erlerobot/smart_motor/AVR_OpenServo_V3-dev/adc.c

/*
    Copyright (c) 2006 Michael P. Thompson <mpthompson@gmail.com>

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
    $Id$
*/

#include <inttypes.h>
#include <avr/io.h>
#include <avr/interrupt.h>

#include "openservo.h"
#include "config.h"
#include "adc.h"
#include "timer.h"

//
// ATmega168
// =========
//
// The 10-bit Analog to Digital Converter (ADC) on the ATmega MCU is used
// to provide power and position feedback from the servo circuitry.  The
// analog inputs are assigned as follows:
//
//  ADC0 (PC0) - Motor Current
//  ADC1 (PC1) - Battery Voltage
//  ADC2 (PC2) - Position
//  ADC3 (PC3) - Temperature
//  ADC7 (PC7) - Back EMF


// Globals used to maintain ADC state and values.
volatile uint8_t adc_power_ready;
volatile uint16_t adc_power_value;
volatile uint8_t adc_position_ready;
volatile uint16_t adc_position_value;
#if BACKEMF_ENABLED
volatile uint8_t adc_backemf_ready;
volatile uint16_t adc_backemf_value;
#endif
#if TEMPERATURE_ENABLED
volatile uint8_t adc_temperature_ready;
volatile uint16_t adc_temperature_value;
#endif

void adc_init(void)
// Initialize ADC conversion for reading current monitoring and position.
{
    // Initialize flags and values.
    adc_power_ready = 0;
    adc_power_value = 0;
    adc_position_ready = 0;
    adc_position_value = 0; 
#if BACKEMF_ENABLED
    adc_backemf_ready = 0;
    adc_backemf_value = 0;
#endif
#if TEMPERATURE_ENABLED
    adc_temperature_ready = 0;
    adc_temperature_value = 0;
#endif

    // Make sure ports PC0 (ADC0), PC1 (ADC1) and PC2 (ADC2) are set low.
    PORTC &= ~((1<<PC0) | (1<<PC1) | (1<<PC2));

    // Disable digital input for ADC0, ADC1 and ADC2.
    DIDR0 |= (1<<ADC0D) | (1<<ADC1D) |(1<<ADC2D);

    // Set the ADC multiplexer selection register.
    ADMUX = (0<<REFS1) | (1<<REFS0) |                       // Select AVCC as voltage reference.
            (0<<ADLAR) |                                    // Keep high bits right adjusted.
            ADC_CHANNEL_POSITION;                           // Position as the first channel to sample.

    // Set the ADC control and status register B.
    ADCSRB = (0<<ADTS2) | (1<<ADTS1) | (1<<ADTS0);          // Timer/Counter0 Compare Match A.

    // Set the ADC control and status register A.
    ADCSRA = (1<<ADEN) |                                    // Enable ADC.
             (0<<ADSC) |                                    // Don't start yet, will be triggered manually.
             (0<<ADATE) |                                   // Don't start auto triggering.
             (1<<ADIE) |                                    // Activate ADC conversion complete interrupt.
             ADPS;											// Prescale -- see above.
}

void adc_start(uint8_t channel)
// Initialise the adc sample on the first channel
{
    // Set the ADC multiplexer selection register.
    ADMUX = (0<<REFS1) | (1<<REFS0) |                       // Select AVCC as voltage reference.
            (0<<ADLAR) |                                    // Keep high bits right adjusted.
            channel;                           // Position as the first channel to sample.

    // Start the ADC reading of the position channel.
    ADCSRA |= (1<<ADSC);
}

SIGNAL(ADC_vect)
// Handles ADC interrupt. This runs as an interrupting self triggering mechanism sampling selected channels
// When interrupted with position, it moved initiates the power sampling, which when interrupted initiates
// the other channels in a chain. The Back EMF is not sampled as part of the
// cascade, as this is handled by the backemf module.
{
    // Read the 10-bit ADC value.
    uint16_t new_value = ADCW;

    // Which channel is being read?
    switch (ADMUX & 0x0f)
    {

        case ADC_CHANNEL_POSITION:

            // Save the new position value.
            adc_position_value = new_value;

            // Flag the position value as ready.
            adc_position_ready = 1;

            // Set the ADC multiplexer selection register.
            ADMUX = (0<<REFS1) | (1<<REFS0) |                       // Select AVCC as voltage reference.
                    (0<<ADLAR) |                                    // Keep high bits right adjusted.
                    ADC_CHANNEL_CURRENT;                            // Power as the next channel to sample.

            // Start the ADC of the power channel now
            ADCSRA |= (1<<ADSC);

            break;


        case ADC_CHANNEL_CURRENT:

            // Save the new power value.
            adc_power_value = new_value;

            // Flag the power value as ready.
            adc_power_ready = 1;

            // Set the ADC multiplexer selection register.
            int channel;

#if TEMPERATURE_ENABLED
            channel = ADC_CHANNEL_TEMPERATURE;                        // Temperature as the next channel to sample.
#elif BATTERY_ENABLED
            channel = ADC_CHANNEL_BATTERY;                            // Sample the battery channel next
#else
            break;
#endif
            ADMUX = (0<<REFS1) | (1<<REFS0) |                       // Select AVCC as voltage reference.
                    (0<<ADLAR) | channel;                           // Keep high bits right adjusted.

            // Start the ADC of the temperature channel now
            ADCSRA |= (1<<ADSC);


            break;

#if TEMPERATURE_ENABLED
        case ADC_CHANNEL_TEMPERATURE:

            // Save the temperature value
            adc_temperature_value = new_value;

            // Fag the temperature value as ready
            adc_temperature_ready = 1;
#if BATTERY_ENABLED
            // Now sample the battery voltage
            // Set the ADC multiplexer selection register.
            ADMUX = (0<<REFS1) | (1<<REFS0) |                       // Select AVCC as voltage reference.
                    (0<<ADLAR) |                                    // Keep high bits right adjusted.
                    ADC_CHANNEL_BATTERY;                            // Battery voltage as the next channel to sample.

            // Start the ADC of the voltage channel now
            ADCSRA |= (1<<ADSC);
#endif
            break;
#endif
#if BATTERY_ENABLED
        case ADC_CHANNEL_BATTERY:

            // Save voltage value to registers
            registers_write_word(REG_VOLTAGE_HI, REG_VOLTAGE_LO, new_value);

            break;
#endif
#if BACKEMF_ENABLED
        case ADC_CHANNEL_BACKEMF:

            adc_backemf_ready = 1;

            adc_backemf_value = new_value;

            break;
#endif
    }
}
