erlerobot/smart_motor/AVR_OpenServo_V3-dev/twi.c

/*
    Copyright (c) 2006 Michael P. Thompson <mpthompson@gmail.com>
        Portions of this code 
    Copyright (c) 2007 Barry Carter <barry.carter@gmail.com>


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
    $Id$
*/

#include <inttypes.h>
#include <avr/io.h>
#include <avr/interrupt.h>

#include "openservo.h"
#include "config.h"
#include "registers.h"
#include "twi.h"
#include "banks.h"

//////////////////////////////////////////////////////////////////
///////////////// Driver Buffer Definitions //////////////////////
//////////////////////////////////////////////////////////////////
// 1,2,4,8,16,32,64,128 or 256 bytes are allowed buffer sizes

#define TWI_RX_BUFFER_SIZE (4)
#define TWI_RX_BUFFER_MASK (TWI_RX_BUFFER_SIZE - 1)

#if (TWI_RX_BUFFER_SIZE & TWI_RX_BUFFER_MASK)
        #error TWI RX buffer size is not a power of 2
#endif

#define TWI_CHK_WRITE_BUFFER_SIZE (16)
#define TWI_CHK_WRITE_BUFFER_MASK (TWI_CHK_WRITE_BUFFER_SIZE - 1)

#if (TWI_CHK_WRITE_BUFFER_SIZE & TWI_CHK_WRITE_BUFFER_MASK)
        #error TWI CHK WRITE buffer size is not a power of 2
#endif

//////////////////////////////////////////////////////////////////

// TWI acknowledgment values.
#define TWI_ACK                             (0x00)
#define TWI_NAK                             (0x01)

// Data state values.
#define TWI_DATA_STATE_COMMAND              (0x00)
#define TWI_DATA_STATE_DATA                 (0x01)
#if TWI_CHECKED_ENABLED
#define TWI_DATA_STATE_CHECKED_COUNTING     (0x02)
#define TWI_DATA_STATE_CHECKED_ADDRESS      (0x03)
#define TWI_DATA_STATE_CHECKED_DATA         (0x04)
#endif

static volatile uint8_t twi_address;
static volatile uint8_t twi_data_state;
static volatile uint8_t twi_overflow_state;

static volatile uint8_t twi_rxhead;
static volatile uint8_t twi_rxtail;
static uint8_t twi_rxbuf[TWI_RX_BUFFER_SIZE];

#if TWI_CHECKED_ENABLED
// For checked writing send in the format of  [i2c addr][0x81][data length][data address][data]...[data] [checksum value] [checksum value]
// For a checked read use  [i2c_addr][0x81][data length][data address] SLA+R [data][data]...[checksum value]
// Checksum is defined as data length + data_address + data[n]
// To verify a write was successful, write the header above, and see if it nacks. nack is failure of checksum.
static uint8_t twi_chk_count;            // current byte in transaction
static uint8_t twi_chk_count_target;     // How many bytes are we reading/writing
static uint8_t twi_chk_sum;              // Accumulator for checksum
static uint8_t twi_chk_write_buffer[TWI_CHK_WRITE_BUFFER_SIZE];
#endif

static uint8_t twi_registers_read(uint8_t address)
// Read the byte from the specified register.  This function handles the
// reading of special registers such as unused registers, redirect and
// redirected registers.
{
    // Mask the most significant bit of the address.
    address &= 0x7F;

    // Are we reading a normal register?
    if (address <= MAX_WRITE_PROTECT_REGISTER)
    {
#if ROLLING_SUBTYPE
        if (address == REG_DEVICE_SUBTYPE)
        {
            return registers_subtype_cycle();
        }
#endif
        // Yes. Complete the read.
        return registers_read_byte(address);
    }

    // Are we reading an unused register.
    if (address <= MAX_UNUSED_REGISTER)
    {
        // Block the read.
        return 0;
    }

    // Are we reading a bank register? 
    if (address <= MAX_BANK_REGISTER)
    {
        // Conditional bank functions
        switch(banks_selected_bank())
        {
            case REDIRECTED_BANK:
                // Are we reading a redirect register.
                if (address <=  MIN_BANK_REGISTER + MAX_REDIRECT_REGISTER)
                {
                    // Yes. Complete the read.
                    return banks_read_byte(REDIRECTED_BANK, address -  MIN_BANK_REGISTER);
                }

                // Are we reading a redirected register?
                if (address <= MIN_BANK_REGISTER + MAX_REDIRECTED_REGISTER)
                {
                    // Adjust address to reference appropriate redirect register.
                    address = address - (MIN_BANK_REGISTER + MIN_REDIRECTED_REGISTER);
                    // Get the address from the redirect register.
                    address = banks_read_byte(REDIRECTED_BANK, address);
                    // Prevent infinite recursion.
                    if (address <= MIN_BANK_REGISTER + MAX_REDIRECT_REGISTER)
                    {
                        // Recursively read redirected address.
                        return twi_registers_read(address);
                    }
                }
                break;
            default:
                break;
        }
        // Defaults to returning the register n the bank array
        return banks_read_byte(banks_selected_bank(), address-MIN_BANK_REGISTER);
    }

    // All other reads are blocked.
    return 0;
}


static void twi_registers_write(uint8_t address, uint8_t data)
// Write non-write protected registers.  This function handles the
// writing of special registers such as unused registers, redirect and
// redirected registers.
{
    // Mask the most significant bit of the address.
    address &= 0x7F;

    // Are we writing a read only register?
    if (address <= MAX_READ_ONLY_REGISTER)
    {
        // Yes. Block the write.
        return;
    }

    // Are we writing a read/write register?
    if (address <= MAX_READ_WRITE_REGISTER)
    {
        // Check that the bank selection is in range
        if (address == REG_BANK_SELECT)
        {
            if (data >= MAX_BANKS)
            {
                // Set the bank number to the maximum
                data = MAX_BANKS-1;
            }
        }

        // Yes. Complete the write.
        registers_write_byte(address, data);

        return;
    }

    // Is writing to the upper registers disabled?
    if (registers_is_write_disabled() && (address <= MAX_WRITE_PROTECT_REGISTER))
    {
        // Yes. Block the write.
        return;
    }

    // Are we writing a write protected register?
    if (address <= MAX_WRITE_PROTECT_REGISTER)
    {
        // Yes. Complete the write if writes are enabled.
        registers_write_byte(address, data);

        return;
    }

    // Are we writing an unused register.
    if (address <= MAX_UNUSED_REGISTER)
    {
        // Yes. Block the write.
        return;
    }

    //TODO check to see if we have writes enabled/disabled
    // Are we writing a bank register? 
    if (address <= MAX_BANK_REGISTER)
    {
        switch(banks_selected_bank())
        {
            case BANK_0:
                break;
            case BANK_1:
                // Are we writing to the configuration bank while writes are disabled?
                if (registers_is_write_disabled())
                    return;
                break;
            case REDIRECTED_BANK:

                // Are we writing a redirect register.
                if (address <= MIN_BANK_REGISTER + MAX_REDIRECT_REGISTER)
                {
                    // Yes. Complete the write.
                    banks_write_byte(REDIRECTED_BANK, address - MIN_BANK_REGISTER, data);

                    return;
                }

                // Are we writing a redirected register?
                if (address <= MIN_BANK_REGISTER + MAX_REDIRECTED_REGISTER)
                {
                    // Adjust address to reference appropriate redirect register.
                    address = address - (MIN_BANK_REGISTER + MIN_REDIRECTED_REGISTER);

                    // Get the address from the redirect register.
                    address = banks_read_byte(REDIRECTED_BANK, address);

                    // Prevent infinite recursion.
                    if (address <= MIN_BANK_REGISTER + MAX_REDIRECT_REGISTER)
                    {
                        // Recursively write redirected address.
                        twi_registers_write(address, data);

                        return;
                    }
                }
                break;
            default:
                break;
        }
        return banks_write_byte(banks_selected_bank(), address-MIN_BANK_REGISTER, data);
    }

    // All other writes are blocked.
    return;
}


#if TWI_CHECKED_ENABLED
static void twi_write_buffer(void)
// Write the recieve buffer to memory.
{
    // Loop over the data within the write buffer.
    for (twi_chk_count = 0; twi_chk_count < twi_chk_count_target; twi_chk_count++)
    {
        // Write the data to the addressed register.
        twi_registers_write(twi_address, twi_chk_write_buffer[twi_chk_count & TWI_CHK_WRITE_BUFFER_MASK]);

        // Increment to the next address.
        ++twi_address;
    }
}
#endif


static uint8_t twi_read_data()
// Handle checked/non-checked read of data.
{
    // By default read the data to be returned.
    uint8_t data = twi_registers_read(twi_address);

#if TWI_CHECKED_ENABLED
    // Are we handling checked data?
    if (twi_data_state == TWI_DATA_STATE_CHECKED_DATA)
    {
        // Have we reached the end of the read?
        if (twi_chk_count < twi_chk_count_target)
        {
            // Add the data to the check sum.
            twi_chk_sum += data;

            // Increment the check sum data count.
            ++twi_chk_count;

            // Increment the address.
            ++twi_address;
        }
        else
        {
            // Replace the data with the checksum.
            data = twi_chk_sum;
        }
    }
    else
    {
        // Increment the address.
        ++twi_address;
    }
#else
    // Increment the address.
    ++twi_address;
#endif

    return data;
}


static uint8_t twi_write_data(uint8_t data)
// Handle checked/non-checked write of data or command.
{
    // By default, return ACK from write.
    uint8_t ack = TWI_ACK;

    // Handle the write depending on the write state.
    switch (twi_data_state)
    {
        case TWI_DATA_STATE_COMMAND:

            // This is a byte.
            if (data < TWI_CMD_RESET)
            {
                // Capture the address.
                twi_address = data;

                // Update the write state.
                twi_data_state = TWI_DATA_STATE_DATA;
            }
#if TWI_CHECKED_ENABLED
            else if (data == TWI_CMD_CHECKED_TXN)
            {
                // Update the write state.
                twi_data_state = TWI_DATA_STATE_CHECKED_COUNTING;
            }
#endif
            else
            {
                // Handle the command asynchronously.
                twi_rxhead = (twi_rxhead + 1) & TWI_RX_BUFFER_MASK;
                twi_rxbuf[twi_rxhead] = data;
            }

            break;

        case TWI_DATA_STATE_DATA:

            // Write the data to the addressed register.
            twi_registers_write(twi_address, data);

            // Increment to the next address.
            ++twi_address;

            break;

#if TWI_CHECKED_ENABLED
        case TWI_DATA_STATE_CHECKED_COUNTING:

            // Read in the count (Make sure it's less than the max count)
            // and start the checksum
            twi_chk_sum = twi_chk_count_target = data & TWI_CHK_WRITE_BUFFER_MASK;

            // Clear the checksum and count.
            twi_chk_count = 0;

            // Update the write state.
            twi_data_state = TWI_DATA_STATE_CHECKED_ADDRESS;

            break;

        case TWI_DATA_STATE_CHECKED_ADDRESS:

            // Capture the address and include it in the checksum
            twi_chk_sum += twi_address = data;

            // Update the write state.
            twi_data_state = TWI_DATA_STATE_CHECKED_DATA;

            break;

        case TWI_DATA_STATE_CHECKED_DATA:

            // Have we reached the end of the write?
            if (twi_chk_count < twi_chk_count_target)
            {
                // No. Write the data to the checksum buffer
                twi_chk_write_buffer[twi_chk_count & TWI_CHK_WRITE_BUFFER_MASK] = data;

                // Add the data to the checksum.
                twi_chk_sum += data;

                // Increment the check sum data count.
                ++twi_chk_count;
            }
            else
            {
                // Verify the checksum
                if (data == twi_chk_sum)
                {
                    // Write the checksum buffer to addressed registers.
                    twi_write_buffer();
                }
                else
                {
                    // Checksum failed so return NACK.
                    ack = TWI_NAK;
                }
            }

            break;
#endif
    }

    return ack;
}

// General call functions. General call allows you to send a data packet to all 
// servos at the same time. In order to use the general call support of the AVR you 
// address the OpenServos at address 0x00. Every servo will respond to the general
// call request and act appropriately. 
// You can specify groups to use with the broadcast request to allow for the servo
// to respond to different requests, or you can allow all to respond to a single
// request.

void general_call_enable(void)
// Enable general call broadcast support at address 0x00
{
    TWAR |=  (1<<TWGCE);       // Enable general call at address 0x00

    uint8_t flags_lo = registers_read_byte(REG_FLAGS_LO);

    // Enable PWM to the servo motor.
    registers_write_byte(REG_FLAGS_LO, flags_lo | (1<<FLAGS_LO_GENERALCALL_ENABLED));
}

void general_call_disable(void)
// Disable general call support.
{
    TWAR &= ~(1<<TWGCE);                      // disable general call

    uint8_t flags_lo = registers_read_byte(REG_FLAGS_LO);

    registers_write_byte(REG_FLAGS_LO, flags_lo  & ~(1<<FLAGS_LO_GENERALCALL_ENABLED));
}

void general_call_start_reset(void)
// Remove the flag that waits for the broadcast request
{
    uint8_t flags_lo = registers_read_byte(REG_FLAGS_LO);

    // Disable the general call wait flag
    registers_write_byte(REG_FLAGS_LO, flags_lo  & ~(1<<FLAGS_LO_GENERALCALL_START));

    // reset the group call register
    registers_write_byte(REG_GENERAL_CALL_GROUP_START, 0);
}

void general_call_start_move(void)
// Start the move by broadcasting at address 0x00
{
    uint8_t flags_lo = registers_read_byte(REG_FLAGS_LO);

    registers_write_byte(REG_FLAGS_LO, flags_lo | (1<<FLAGS_LO_GENERALCALL_START));
}

void general_call_start_wait(void)
// Set the servo into wait mode. We will wait for the broadcast before move
{
    uint8_t flags_lo = registers_read_byte(REG_FLAGS_LO);

    registers_write_byte(REG_FLAGS_LO, flags_lo | (1<<FLAGS_LO_GENERALCALL_WAIT));
}

void general_call_start_wait_reset(void)
// Disable the start wait state. Returns servo to normal operation.
{
    uint8_t flags_lo = registers_read_byte(REG_FLAGS_LO);

    registers_write_byte(REG_FLAGS_LO, flags_lo  & ~(1<<FLAGS_LO_GENERALCALL_WAIT));
}

void
twi_slave_init(uint8_t slave_address)
// Initialise USI for TWI slave mode.
{
    // Flush the buffers.
    twi_rxtail = 0;
    twi_rxhead = 0;

    // Set own TWI slave address.
    TWAR = slave_address << 1;

    // Initialise General call
    general_call_disable();
    general_call_start_reset();
    general_call_start_wait_reset();

    // Default content = SDA released.
    TWDR = 0xFF;

    // Initialize the TWI interrupt to wait for a new event.
    TWCR = (1<<TWEN) |                                  // Keep the TWI interface enabled.
           (1<<TWIE) |                                  // Keep the TWI interrupt enabled.
           (0<<TWSTA) |                                 // Don't generate start condition.
           (0<<TWSTO) |                                 // Don't generate stop condition.
           (1<<TWINT) |                                 // Clear the TWI interrupt.
           (1<<TWEA) |                                  // Acknowledge the data.
           (0<<TWWC);                                   //
}


uint8_t twi_receive_byte(void)
// Returns a byte from the receive buffer. Waits if buffer is empty.
{
    // Wait for data in the buffer.
    while (twi_rxhead == twi_rxtail);

    // Calculate buffer index.
    twi_rxtail = (twi_rxtail + 1 ) & TWI_RX_BUFFER_MASK;

    // Return data from the buffer.
    return twi_rxbuf[twi_rxtail];
}


uint8_t twi_data_in_receive_buffer(void)
// Check if there is data in the receive buffer.
{
    // Return 0 (FALSE) if the receive buffer is empty.
    return (twi_rxhead != twi_rxtail);
}


SIGNAL(TWI_vect)
// Handle the TWI interrupt condition.
{
    switch (TWSR)
    {
        // Own SLA+R has been received; ACK has been returned.
        case TWI_STX_ADR_ACK:
        // Data byte in TWDR has been transmitted; ACK has been received.
        case TWI_STX_DATA_ACK:

            // Read the checked/non-checked data.
            TWDR = twi_read_data();

            // Data byte will be transmitted and ACK should be received.
            TWCR = (1<<TWEN) |                              // Keep the TWI interface enabled.
                   (1<<TWIE) |                              // Keep the TWI interrupt enabled.
                   (0<<TWSTA) |                             // Don't generate start condition.
                   (0<<TWSTO) |                             // Don't generate stop condition.
                   (1<<TWINT) |                             // Clear the TWI interrupt.
                   (1<<TWEA) |                              // Acknowledge the data.
                   (0<<TWWC);                               //
            break;

        // Data byte in TWDR has been transmitted; NOT ACK has been received.
        case TWI_STX_DATA_NACK:
        // Last data byte in TWDR has been transmitted (TWEA = "0"); ACK has been received.
        case TWI_STX_DATA_ACK_LAST_BYTE:

            // Switched to the not addressed slave mode; own SLA will be recognized.
            TWCR = (1<<TWEN) |                              // Keep the TWI interface enabled.
                   (1<<TWIE) |                              // Keep the TWI interrupt enabled.
                   (0<<TWSTA) |                             // Don't generate start condition.
                   (0<<TWSTO) |                             // Don't generate stop condition.
                   (1<<TWINT) |                             // Clear the TWI interrupt.
                   (1<<TWEA) |                              // Acknowledge the data.
                   (0<<TWWC);                               //
            break;

        // Own SLA+W has been received; ACK has been returned.
        case TWI_SRX_ADR_ACK:
        // General call GEN+W received; ACK has been returned
        case TWI_SRX_GEN_ACK:

            // Reset the data state.
            twi_data_state = TWI_DATA_STATE_COMMAND;

            // Data byte will be received and ACK will be returned.
            TWCR = (1<<TWEN) |                              // Keep the TWI interface enabled.
                   (1<<TWIE) |                              // Keep the TWI interrupt enabled.
                   (0<<TWSTA) |                             // Don't generate start condition.
                   (0<<TWSTO) |                             // Don't generate stop condition.
                   (1<<TWINT) |                             // Clear the TWI interrupt.
                   (1<<TWEA) |                              // Acknowledge the data.
                   (0<<TWWC);                               //

            break;

        // Previously addressed with own SLA+W; data has been received; ACK has been returned.
        case TWI_SRX_ADR_DATA_ACK:
        // Previously addressed with general call SLA+W; data has been received; ACK has been returned.
        case TWI_SRX_GEN_DATA_ACK:

            // Write the data.
            if (twi_write_data(TWDR) == TWI_ACK)
            {
                // Next data byte will be received and ACK will be returned.
                TWCR = (1<<TWEN) |                          // Keep the TWI interface enabled.
                       (1<<TWIE) |                          // Keep the TWI interrupt enabled.
                       (0<<TWSTA) |                         // Don't generate start condition.
                       (0<<TWSTO) |                         // Don't generate stop condition.
                       (1<<TWINT) |                         // Clear the TWI interrupt.
                       (1<<TWEA) |                          // Acknowledge the data.
                       (0<<TWWC);                           //
            }
            else
            {
                // Next data byte will not be received and NACK will be returned.
                TWCR = (1<<TWEN) |                          // Keep the TWI interface enabled.
                       (1<<TWIE) |                          // Keep the TWI interrupt enabled.
                       (0<<TWSTA) |                         // Don't generate start condition.
                       (0<<TWSTO) |                         // Don't generate stop condition.
                       (1<<TWINT) |                         // Clear the TWI interrupt.
                       (0<<TWEA) |                          // Don't Acknowledge the data.
                       (0<<TWWC);                           //
            }

            break;

        // Previously addressed with own SLA+W; data has been received; NOT ACK has been returned.
        case TWI_SRX_ADR_DATA_NACK:
        // A STOP condition or repeated START condition has been received while still addressed as Slave.
        case TWI_SRX_STOP_RESTART:
        // Previously addressed with general call; data has been received; NOT ACK has been returned
        case TWI_SRX_GEN_DATA_NACK:

             // Switch to the not addressed slave mode; own SLA will be recognized.
             TWCR = (1<<TWEN) |                              // Keep the TWI interface enabled.
                    (1<<TWIE) |                              // Keep the TWI interrupt enabled.
                    (0<<TWSTA) |                             // Don't generate start condition.
                    (0<<TWSTO) |                             // Don't generate stop condition.
                    (1<<TWINT) |                             // Clear the TWI interrupt.
                    (1<<TWEA) |                              // Acknowledge the data.
                    (0<<TWWC);                               //

            break;

        // Bus error due to an illegal START or STOP condition.
        case TWI_BUS_ERROR:

            // Only the internal hardware is affected, no STOP condition is sent on the bus.
            // In all cases, the bus is released and TWSTO is cleared.
            TWCR = (1<<TWEN) |                              // Keep the TWI interface enabled.
                   (1<<TWIE) |                              // Keep the TWI interrupt enabled.
                   (0<<TWSTA) |                             // Don't generate start condition.
                   (1<<TWSTO) |                             // Don't generate stop condition.
                   (1<<TWINT) |                             // Clear the TWI interrupt.
                   (1<<TWEA) |                              // Acknowledge the data.
                   (0<<TWWC);                               //
            break;

        // No relevant state information available; TWINT="0".
        case TWI_NO_STATE:

            // No action required.
            break;

        default:

            // Reset the TWI interrupt to wait for a new event.
            TWCR = (1<<TWEN) |                                  // Keep the TWI interface enabled.
                   (1<<TWIE) |                                  // Keep the TWI interrupt enabled.
                   (0<<TWSTA) |                                 // Don't generate start condition.
                   (0<<TWSTO) |                                 // Don't generate stop condition.
                   (1<<TWINT) |                                 // Clear the TWI interrupt.
                   (1<<TWEA) |                                  // Acknowledge the data.
                   (0<<TWWC);                                   //
            break;
    }
}
