erlerobot/smart_motor/Timer/src/ads1115.h

/**
 *  project  : 	RPI_SmartServo			
 * 	
 * 	@file ads1115.h
 *  @brief Header for the ads1115 adc converter module.
 * 
 *  @note 
 *
 *  	none
 *
 *  \code
 *  MODIFICATION HISTORY:
 *
 *  Ver   Who        Date        Changes
 *  ----- ---------- ----------  -------------------------------------
 *  1.00 jlamperez  6/3/2016  First release
 * 
 *  \endcode
 *
 *	Copyright (c) 2016, Jorge Lampérez. All rights reserved.
 */

#ifndef ADS1115_H_
#define ADS1115_H_ 1

#include <stdint.h>

/*=========================================================================
    I2C ADDRESS/BITS
    -----------------------------------------------------------------------*/
    #define ADS1115_ADDRESS                 (0x48)    // 1001 000 (ADDR = GND)
/*=========================================================================*/

/*=========================================================================
    SINGLE ENDED CHANNEL
    -----------------------------------------------------------------------*/
    #define POSITION_CHANNEL                (0x0)    // 
    #define TEMP_CHANNEL                    (0x1)    //
    #define CURRENT_CHANNEL                 (0x2)    //
    #define BATTERY_CHANNEL                 (0x3)    //
/*=========================================================================*/

/*=========================================================================
    POINTER REGISTER
    -----------------------------------------------------------------------*/
    #define ADS1115_REG_POINTER_MASK        (0x03)
    #define ADS1115_REG_POINTER_CONVERT     (0x00)
    #define ADS1115_REG_POINTER_CONFIG      (0x01)
    #define ADS1115_REG_POINTER_LOWTHRESH   (0x02)
    #define ADS1115_REG_POINTER_HITHRESH    (0x03)
/*=========================================================================*/

/*=========================================================================
    CONFIG REGISTER
    -----------------------------------------------------------------------*/
    #define ADS1115_REG_CONFIG_OS_MASK      (0x8000)
    #define ADS1115_REG_CONFIG_OS_SINGLE    (0x8000)  // Write: Set to start a single-conversion
    #define ADS1115_REG_CONFIG_OS_BUSY      (0x0000)  // Read: Bit = 0 when conversion is in progress
    #define ADS1115_REG_CONFIG_OS_NOTBUSY   (0x8000)  // Read: Bit = 1 when device is not performing a conversion

    #define ADS1115_REG_CONFIG_MUX_MASK     (0x7000)
    #define ADS1115_REG_CONFIG_MUX_DIFF_0_1 (0x0000)  // Differential P = AIN0, N = AIN1 
    #define ADS1115_REG_CONFIG_MUX_DIFF_0_3 (0x1000)  // Differential P = AIN0, N = AIN3
    #define ADS1115_REG_CONFIG_MUX_DIFF_1_3 (0x2000)  // Differential P = AIN1, N = AIN3
    #define ADS1115_REG_CONFIG_MUX_DIFF_2_3 (0x3000)  // Differential P = AIN2, N = AIN3
    #define ADS1115_REG_CONFIG_MUX_SINGLE_0 (0x4000)  // Single-ended AIN0
    #define ADS1115_REG_CONFIG_MUX_SINGLE_1 (0x5000)  // Single-ended AIN1
    #define ADS1115_REG_CONFIG_MUX_SINGLE_2 (0x6000)  // Single-ended AIN2
    #define ADS1115_REG_CONFIG_MUX_SINGLE_3 (0x7000)  // Single-ended AIN3

    #define ADS1115_REG_CONFIG_PGA_MASK     (0x0E00)
    #define ADS1115_REG_CONFIG_PGA_6_144V   (0x0000)  // +/-6.144V range = Gain 2/3
    #define ADS1115_REG_CONFIG_PGA_4_096V   (0x0200)  // +/-4.096V range = Gain 1
    #define ADS1115_REG_CONFIG_PGA_2_048V   (0x0400)  // +/-2.048V range = Gain 2 
    #define ADS1115_REG_CONFIG_PGA_1_024V   (0x0600)  // +/-1.024V range = Gain 4
    #define ADS1115_REG_CONFIG_PGA_0_512V   (0x0800)  // +/-0.512V range = Gain 8
    #define ADS1115_REG_CONFIG_PGA_0_256V   (0x0A00)  // +/-0.256V range = Gain 16

    #define ADS1115_REG_CONFIG_MODE_MASK    (0x0100)
    #define ADS1115_REG_CONFIG_MODE_CONTIN  (0x0000)  // Continuous conversion mode
    #define ADS1115_REG_CONFIG_MODE_SINGLE  (0x0100)  // Power-down single-shot mode 

    #define ADS1115_REG_CONFIG_DR_MASK      (0x00E0)  
    #define ADS1115_REG_CONFIG_DR_8SPS      (0x0000)  // 8 samples per second
    #define ADS1115_REG_CONFIG_DR_16SPS     (0x0020)  // 16 samples per second
    #define ADS1115_REG_CONFIG_DR_32SPS     (0x0040)  // 32 samples per second
    #define ADS1115_REG_CONFIG_DR_64SPS     (0x0060)  // 64 samples per second
    #define ADS1115_REG_CONFIG_DR_128SPS    (0x0080)  // 128 samples per second 
    #define ADS1115_REG_CONFIG_DR_250SPS    (0x00A0)  // 250 samples per second
    #define ADS1115_REG_CONFIG_DR_475SPS    (0x00C0)  // 475 samples per second
    #define ADS1115_REG_CONFIG_DR_860SPS    (0x00E0)  // 860 samples per second


    #define ADS1115_REG_CONFIG_CMODE_MASK   (0x0010)
    #define ADS1115_REG_CONFIG_CMODE_TRAD   (0x0000)  // Traditional comparator with hysteresis 
    #define ADS1115_REG_CONFIG_CMODE_WINDOW (0x0010)  // Window comparator

    #define ADS1115_REG_CONFIG_CPOL_MASK    (0x0008)
    #define ADS1115_REG_CONFIG_CPOL_ACTVLOW (0x0000)  // ALERT/RDY pin is low when active 
    #define ADS1115_REG_CONFIG_CPOL_ACTVHI  (0x0008)  // ALERT/RDY pin is high when active

    #define ADS1115_REG_CONFIG_CLAT_MASK    (0x0004)  // Determines if ALERT/RDY pin latches once asserted
    #define ADS1115_REG_CONFIG_CLAT_NONLAT  (0x0000)  // Non-latching comparator 
    #define ADS1115_REG_CONFIG_CLAT_LATCH   (0x0004)  // Latching comparator

    #define ADS1115_REG_CONFIG_CQUE_MASK    (0x0003)
    #define ADS1115_REG_CONFIG_CQUE_1CONV   (0x0000)  // Assert ALERT/RDY after one conversions
    #define ADS1115_REG_CONFIG_CQUE_2CONV   (0x0001)  // Assert ALERT/RDY after two conversions
    #define ADS1115_REG_CONFIG_CQUE_4CONV   (0x0002)  // Assert ALERT/RDY after four conversions
    #define ADS1115_REG_CONFIG_CQUE_NONE    (0x0003)  // Disable the comparator and put ALERT/RDY in high state 
/*=========================================================================*/
    
/**
	Initialization of the ads1115 adc module.
*/
void ADS1115_init(uint8_t address);
/**
	Set the ads1115 gain
*/
void ADS1115_setGain(uint16_t gain);
/**
	Get the ads1115 gain
*/
uint16_t ADS1115_getGain();
/**
	Read the ADC value in singleEnded mode. 4 channels are posible in this mode.
*/
uint16_t ADS1115_readADC_singleEnded(uint8_t channel);

#endif
