erlerobot/smart_motor/RPI_SmartServo/Framework/modules/adc.c

/**
 *  project  : 	RPI_SmartServo			
 * 	
 * 	@file adc.c
 *  @brief Adc module implementation. It works like an interface for different adc's, now ads1115 adc is used.
 * 
 *  @note 
 *
 *  	none
 *
 *  \code
 *  MODIFICATION HISTORY:
 *
 *  Ver   Who        Date        Changes
 *  ----- ---------- ----------  -------------------------------------
 *  1.00 jlamperez  6/3/2016  First release
 * 
 *  \endcode
 *
 *	Copyright (c) 2016, Jorge Lampérez. All rights reserved.
 */

#include <signal.h>
#include <stdio.h>
#include "adc.h"
#include "ads1115.h"
#include "registers.h"
#include "../../config.h"

volatile uint8_t adc_position_ready;
volatile uint16_t adc_position_value;

/**
 *
 * Initialize ADC conversion.
 *
 * @return	None.
 *
 * @note		ADC used, ADS1115.
 *
 */
void ADC_init() {
#ifdef CONFIG_DEBUGGER
	printf("ADC initialization\n");
#endif
	// Init ADS1115 adc.
	ADS1115_init(ADS1115_ADDRESS);
	// Init module global variables.
	adc_position_ready = 0;
	adc_position_value = 0;
}
/**
 *
 * Read position from ADC.
 *
 * @return	None.
 *
 * @note		None.
 *
 */
void ADC_readPosition() {
#ifdef CONFIG_DEBUGGER
	printf("ADC_readPosition\n");
#endif
	// Read from i2C
	adc_position_value = ADS1115_readADC_singleEnded(POSITION_CHANNEL);
	// Save value in registers position.
	set_position(adc_position_value);
	// Put flag to 1.
	adc_position_ready = 1;
#ifdef CONFIG_DEBUGGER
	printf("ADC position bit: %d \n", adc_position_value);
	float voltage = (adc_position_value*ADC_RES_CONSTANT)/1000; //for 12 bits
	printf("ADC position voltage: %f \n", voltage);
#endif
}
/**
 *
 * Read voltage from ADC
 *
 * @return	None.
 *
 * @note		None.
 *
 */
void ADC_readTemp() {
	uint16_t adc_temp_value;
	adc_temp_value = ADS1115_readADC_singleEnded(TEMP_CHANNEL);
	set_temp(adc_temp_value);

#ifdef CONFIG_DEBUGGER
	printf("ADC Temp bit: %d \n", adc_temp_value);
	float temp = (adc_temp_value * ADC_RES_CONSTANT - 0.4) / 0.0195;
	printf("ADC Temp is:%f ºC\n", temp);
#endif
}
/**
 *
 * Read current from ADC
 *
 * @return	None.
 *
 * @note		None.
 *
 */
void ADC_readCurrent() {
	uint16_t adc_current_value;
	adc_current_value = ADS1115_readADC_singleEnded(CURRENT_CHANNEL);
	set_current(adc_current_value);

#ifdef CONFIG_DEBUGGER
	printf("ADC Current bit: %d \n", adc_current_value);
	float current = (adc_current_value * ADC_RES_CONSTANT) / (0.05 * 4990 * 0.01);
	printf("ADC Current is: %f \n", current);
#endif

}
/**
 *
 * Read battery from ADC
 *
 * @return	None.
 *
 * @note		None.
 *
 */
void ADC_readBattery() {
	uint16_t adc_battery_value;
	adc_battery_value = ADS1115_readADC_singleEnded(BATTERY_CHANNEL);
	set_battery(adc_battery_value);

#ifdef CONFIG_DEBUGGER
	printf("ADC Battery bit: %d \n", adc_battery_value);
	float battery = adc_battery_value * 3.7 * ADC_RES_CONSTANT;
	printf("ADC Battery is: %f \n", battery);
#endif

}
/**
 *
 * ADC handler for the timer signal. Read 16 bit ADC value.
 *
 * @param 	sig
 * @param 	si
 * @param 	uc
 *
 * @return	None.
 *
 * @note		None.
 *
 */
void ADC_handler(int sig, siginfo_t *si, void *uc) {

	// POSITION (Potenciometer)
	ADC_readPosition();
	// CURRENT
	ADC_readCurrent();
	// BATTERY
	ADC_readBattery();
	//VOLTAGE
	ADC_readTemp();
}
