erlerobot/smart_motor/RPI_SmartServo/Framework/modules/pwm.h

/**
 *  project  :  RPI_SmartServo          
 *  
 *  @file pwm.h
 *  @brief Header for pwm module.
 * 
 *  @note 
 *
 *      none
 *
 *  \code
 *  MODIFICATION HISTORY:
 *
 *  Ver   Who        Date        Changes
 *  ----- ---------- ----------  -------------------------------------
 *  1.00 jlamperez  6/3/2016  First release
 * 
 *  \endcode
 *
 *  Copyright (c) 2016, Jorge Lampérez. All rights reserved.
 */

#ifndef PWM_H_
#define PWM_H_ 1

#include <stdint.h>

// Initialize the PWM module for controlling a DC motor
void PWM_init(void);
// Initialize the PWM algorithm related registers values.
void PWM_registers_defaults(void);
// Update PWM signal sent to the motor -255 to -1 cw,
// 1-255 ccw and 0 stop.
void PWM_update(uint16_t position, int16_t pwm);
// Stop all PWM signals to the motor.
void PWM_stop(void);


#endif
